AnmolS-EE/PowerDistributionBoard-PCB/Simulations/Buck_24V_to_5V_Test.asc

C1: cap; 470µ; V=16 Rser=0.05
C2: cap; 0.1µ
C3: cap; 0.1µ
C4: cap; 470µ; V=50 Rser=0.05
C5: cap; 0.01µ
D1: diode; MBRS340
L1: ind; 47µ; Rser=1m
R1: res; 1260
R2: res; 1000
R3: res; 2
R4: res; 2000
U1: LT1074
V1: voltage; 24
Named nets: 0, INPUT, OUTPUT, SW
.tran 50m
