AnmolS-EE/PowerDistributionBoard-PCB/Simulations/LDO_3V3_Test.asc

C1: cap; 10µ; V=50
C2: cap; 22µ; V=50
R1: res; 5
U1: LT1117-3.3
V1: voltage; 5
Named nets: 0, 3.3V_Rail, 5V_Input
.tran 100m
