AnmolS-EE/PowerDistributionBoard-PCB/Simulations/Dynamic_9V_12V_selector.asc

C1: cap; 470µ; V=16 Rser=0.05
C4: cap; 470µ; V=50 Rser=0.05
C5: cap; 0.01µ
D1: diode; MBRS340
L1: ind; 47µ; Rser=1m
M1: nmos; 2N7002
R1: res; 10k
R2: res; 7.9k
R3: res; 2
R4: res; 2000
R5: res; 5.5k
U1: LT1074
V1: voltage; 24
V2: voltage; PULSE(0 3.3 25m 1u 1u 50m)
Named nets: 0, INPUT, OUTPUT
.tran 50m
